doducminh/3d-models-aquarium-mesh-fish-cave/gcode/v9/lotus-body.png

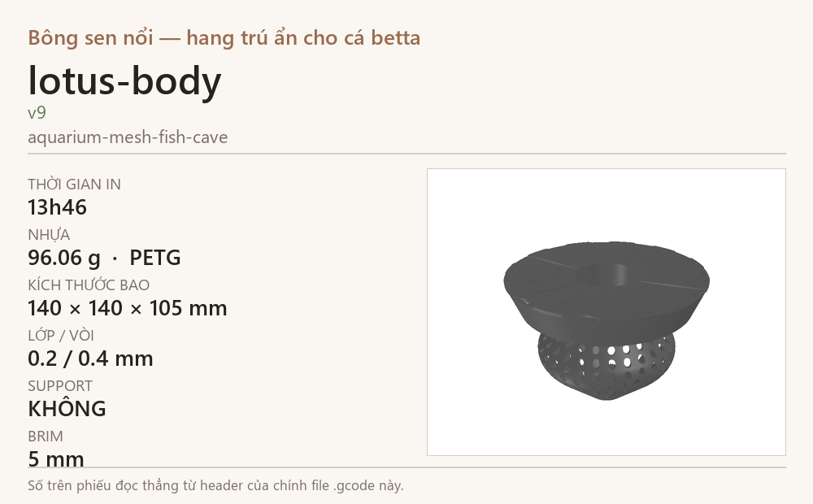
gcode/v9/lotus-body.png
